JoelEB/ApoBoard2017/PreviousYears/DEFCON_Board/hardware/hhv-dcdarknet-display.brd

## EAGLE design PreviousYears/DEFCON_Board/hardware/hhv-dcdarknet-display.brd (2017-04-06, an earlier design)

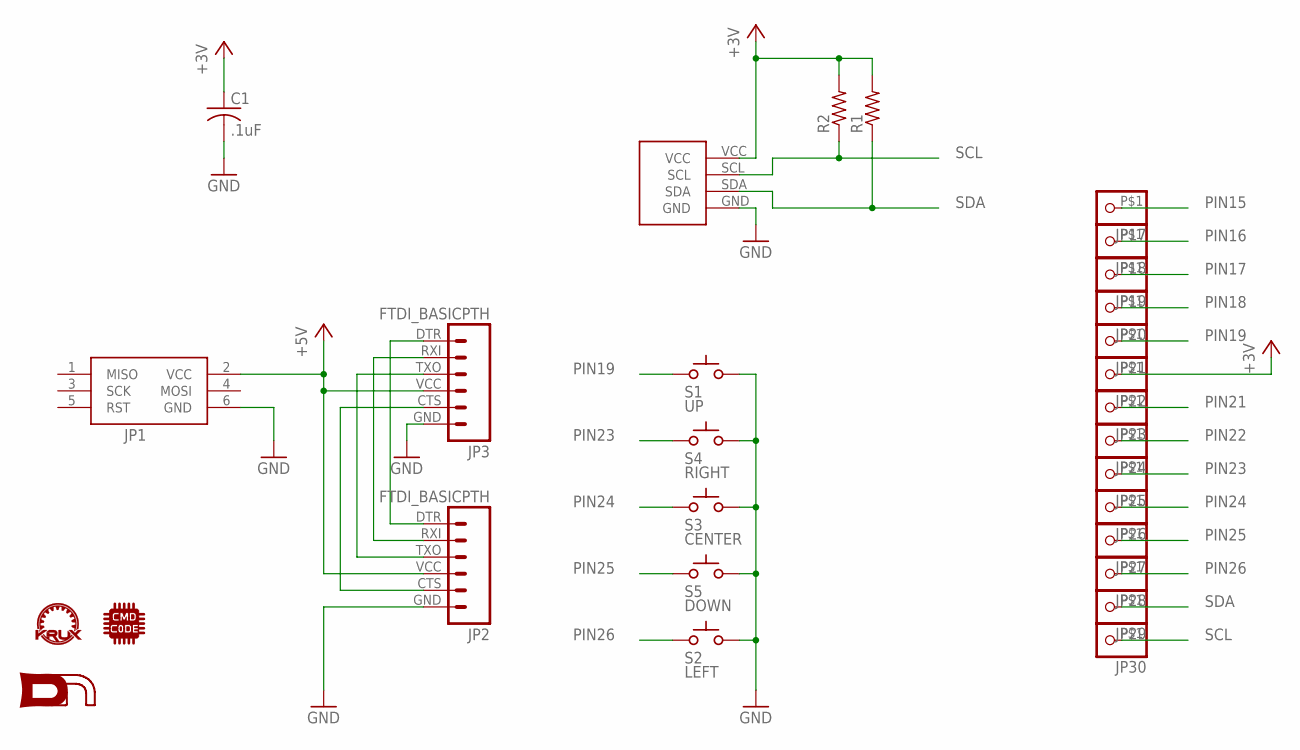
[picture p12: schematic hhv-dcdarknet-display.sch]

Parts:
C1: .1uF; C025-030X050
JP1: JP1; AVRISP
JP2, JP3: FTDI_BASICPTH; FTDI_BASIC
JP17, JP18, JP19, JP20, JP21, JP22, JP23, JP24, JP25, JP26, JP27, JP28, JP29, JP30: PINHD-1X11X1_SQUARE; 1X1-SMALL_CUT
R1, R2: R-US_0204/7; 0204/7
S1: UP; TACTILE-2PIN
S2: LEFT; TACTILE-2PIN
S3: CENTER; TACTILE-2PIN
S4: RIGHT; TACTILE-2PIN
S5: DOWN; TACTILE-2PIN
U$1: KRUX_LOGO
U$2: DN_LOGO
U$3: I2C_0.96_OLEDOLED; I2C_0.96_OLED
U$4: CMDC0DE_LOGO; CMDC0DE

Connections:
+3V3: C1.1, JP22.P$1, R1.2, R2.2, U$3.VCC
+5V: JP1.2 (VCC), JP2.VCC (4), JP3.VCC (4)
GND: C1.2, JP1.6 (GND), JP2.GND (6), JP3.GND (6), S1.P$1 (A), S2.P$1 (A), S3.P$1 (A), S4.P$1 (A), S5.P$1 (A), U$3.GND
unnamed: JP2.DTR (1), JP3.DTR (1)
unnamed: JP2.RXI (2), JP3.RXI (2)
unnamed: JP2.TXO (3), JP3.TXO (3)
unnamed: JP2.CTS (5), JP3.CTS (5)
PIN15: JP17.P$1
PIN16: JP18.P$1
PIN17: JP19.P$1
PIN18: JP20.P$1
PIN19: JP21.P$1, S1.P$2 (C)
PIN21: JP23.P$1
PIN22: JP24.P$1
PIN23: JP25.P$1, S4.P$2 (C)
PIN24: JP26.P$1, S3.P$2 (C)
PIN25: JP27.P$1, S5.P$2 (C)
PIN26: JP28.P$1, S2.P$2 (C)
PIN27: JP29.P$1, R1.1, U$3.SDA
PIN28: JP30.P$1, R2.1, U$3.SCL

Notes on the sheet:
SCL
SDA
PIN26
PIN25
PIN24
PIN23
PIN22
PIN21
PIN19
PIN18
PIN17
PIN16
PIN15

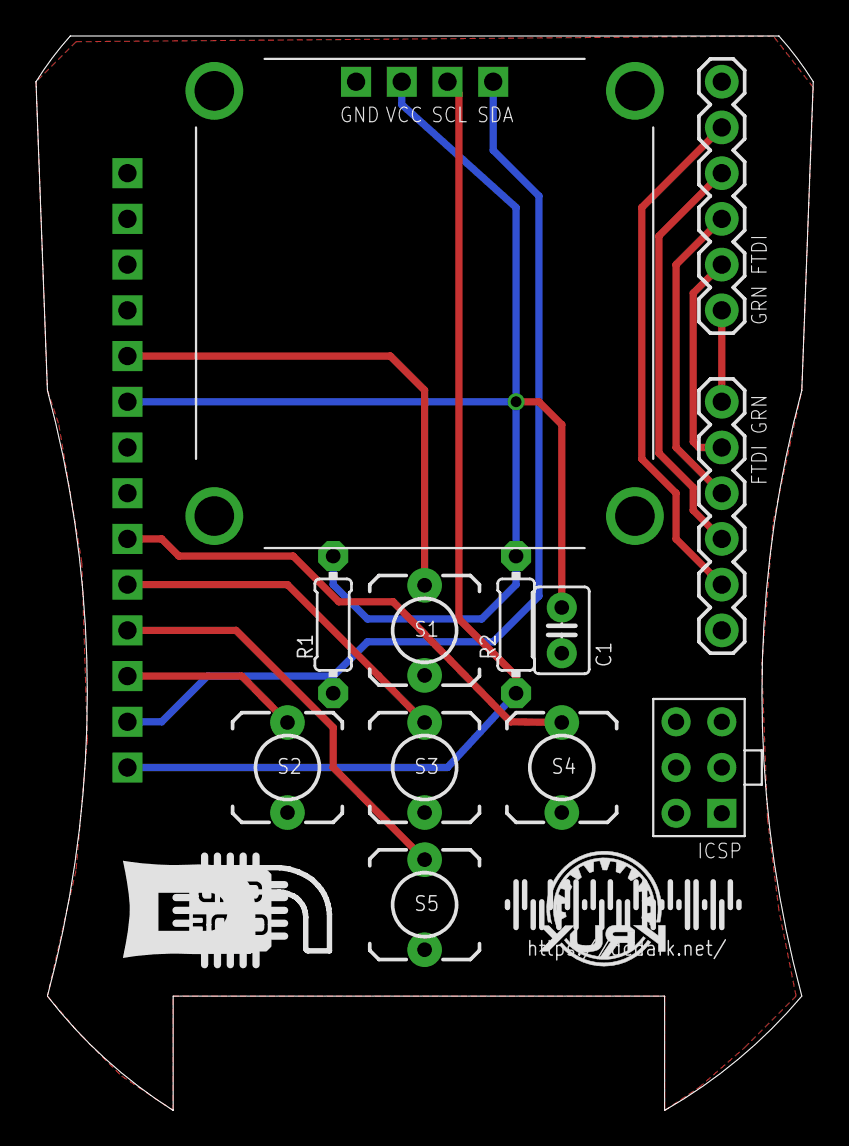
[picture p13: board hhv-dcdarknet-display.brd from above]

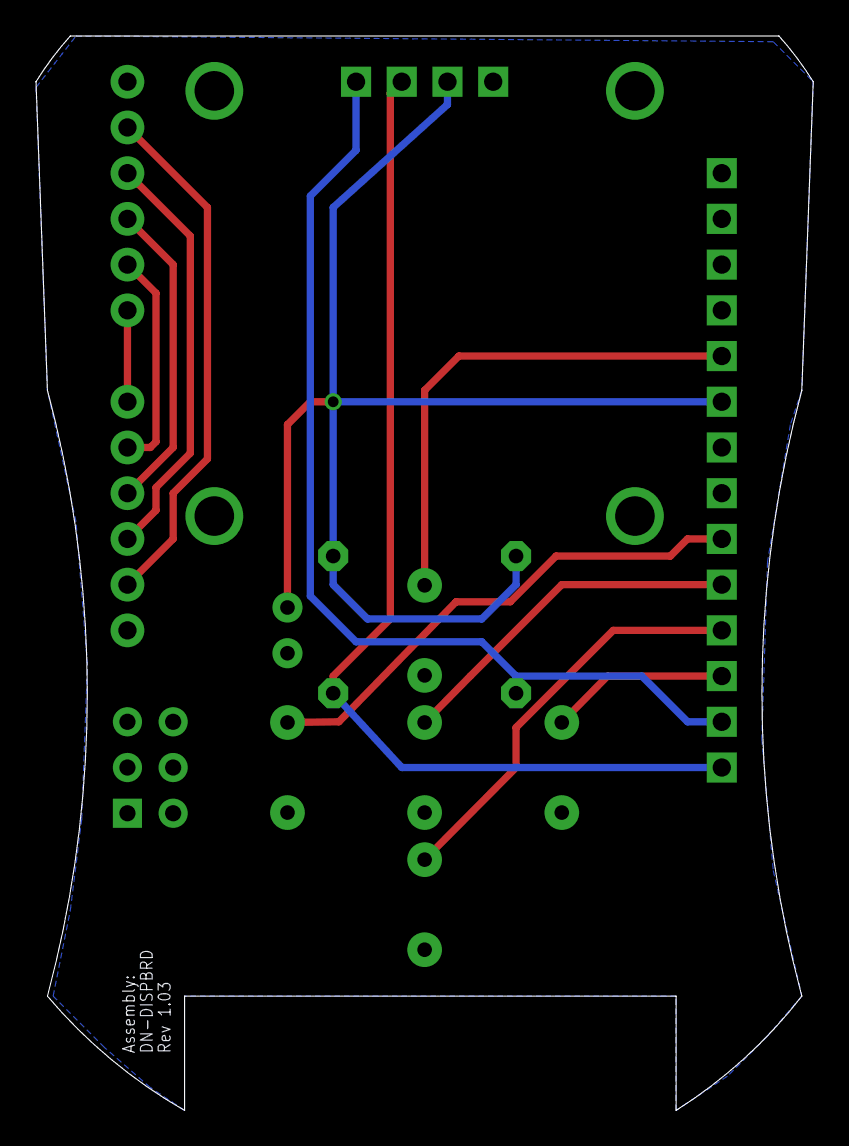
[picture p14: board hhv-dcdarknet-display.brd from below]

Board: 2 copper layers, 43.2 x 59.7 mm, 29 parts (2 on the bottom side), 14 nets.
