JoelEB/ApoBoard2017/PreviousYears/DEFCON_Board/hardware/hhv-dcdarknet-proto.brd

## EAGLE design PreviousYears/DEFCON_Board/hardware/hhv-dcdarknet-proto.brd (2017-04-06, an earlier design)

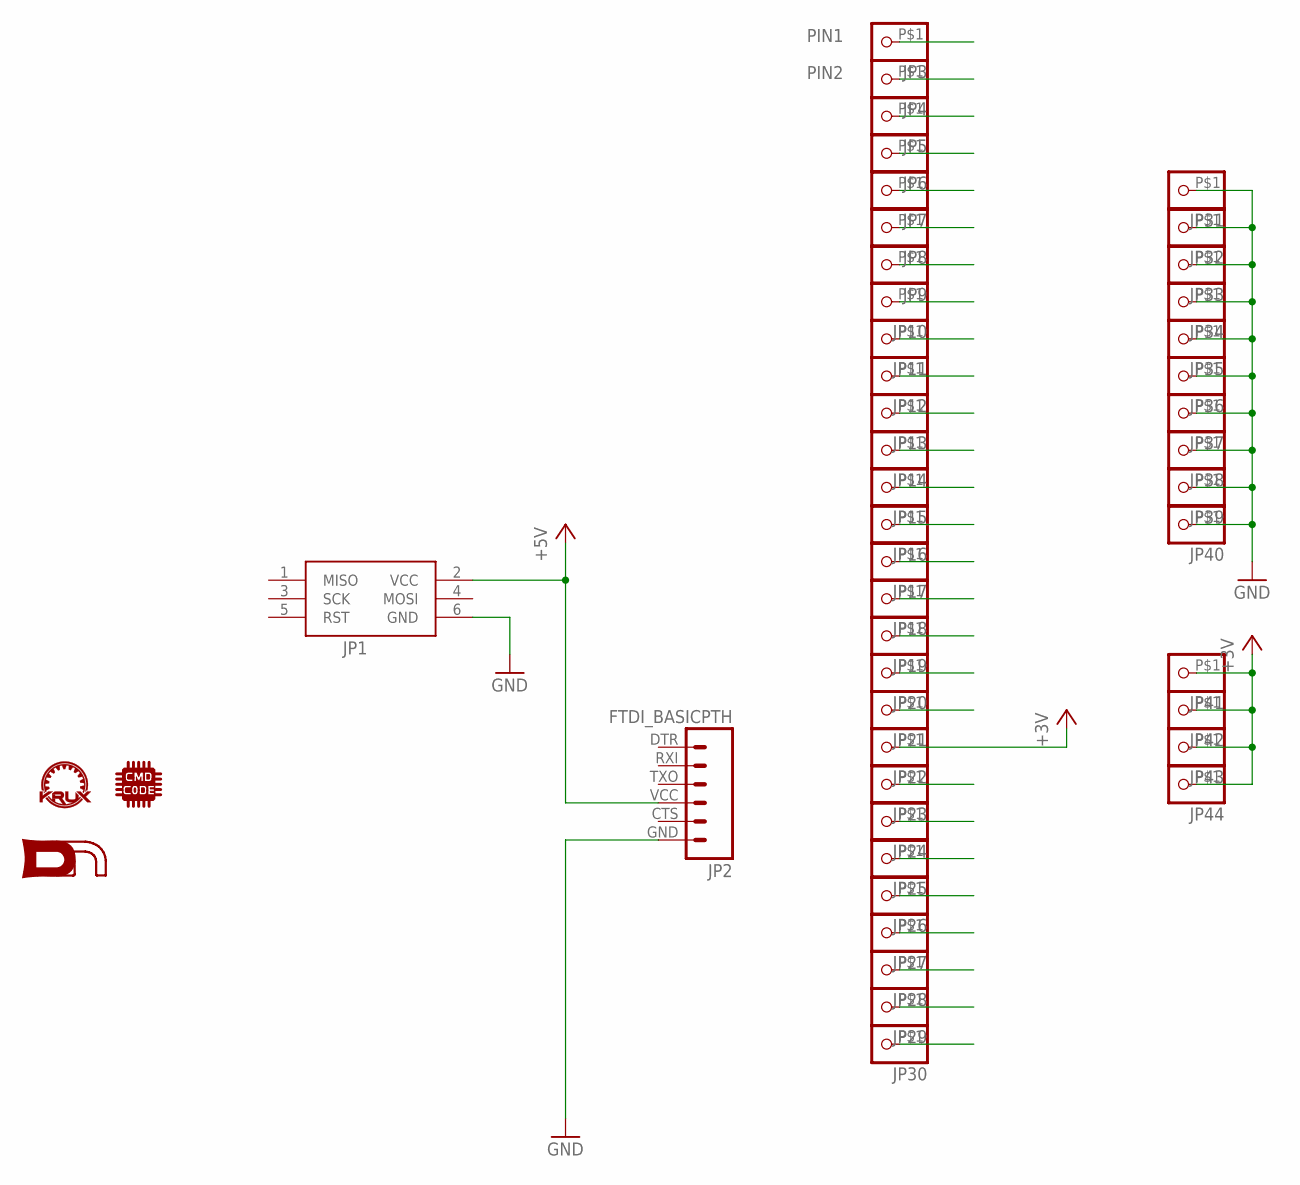
[picture p15: schematic hhv-dcdarknet-proto.sch]

Parts:
JP1: JP1; AVRISP
JP2: FTDI_BASICPTH; FTDI_BASIC
JP3, JP4, JP5, JP6, JP7, JP8, JP9, JP10, JP11, JP12, JP13, JP14, JP15, JP16, JP17, JP18, JP19, JP20, JP21, JP22, JP23, JP24, JP25, JP26, JP27, JP28, JP29, JP30, JP31, JP32, JP33, JP34, JP35, JP36, JP37, JP38, JP39, JP40, JP41, JP42, JP43, JP44: PINHD-1X11X1_SQUARE; 1X1-SMALL_CUT
U$1: KRUX_LOGO
U$2: DN_LOGO
U$3: CMDC0DE_LOGO; CMDC0DE

Connections:
+3V3: JP9.P$1, JP22.P$1, JP41.P$1, JP42.P$1, JP43.P$1, JP44.P$1
+5V: JP1.2 (VCC), JP2.VCC (4)
GND: JP1.6 (GND), JP2.GND (6), JP10.P$1, JP31.P$1, JP32.P$1, JP33.P$1, JP34.P$1, JP35.P$1, JP36.P$1, JP37.P$1, JP38.P$1, JP39.P$1, JP40.P$1
PIN1: JP3.P$1
PIN2: JP4.P$1
PIN3: JP5.P$1
PIN4: JP6.P$1
PIN5: JP7.P$1
PIN6: JP8.P$1
PIN9: JP11.P$1
PIN10: JP12.P$1
PIN11: JP13.P$1
PIN12: JP14.P$1
PIN13: JP15.P$1
PIN14: JP16.P$1
PIN15: JP17.P$1
PIN16: JP18.P$1
PIN17: JP19.P$1
PIN18: JP20.P$1
PIN19: JP21.P$1
PIN21: JP23.P$1
PIN22: JP24.P$1
PIN23: JP25.P$1
PIN24: JP26.P$1
PIN25: JP27.P$1
PIN26: JP28.P$1
PIN27: JP29.P$1
PIN28: JP30.P$1
