JoelEB/ApoBoard2017/PreviousYears/DEFCON_Board/hardware/hhv-dcdarknet-proto.brd

## EAGLE design PreviousYears/DEFCON_Board/hardware/hhv-dcdarknet-proto.brd (continued)

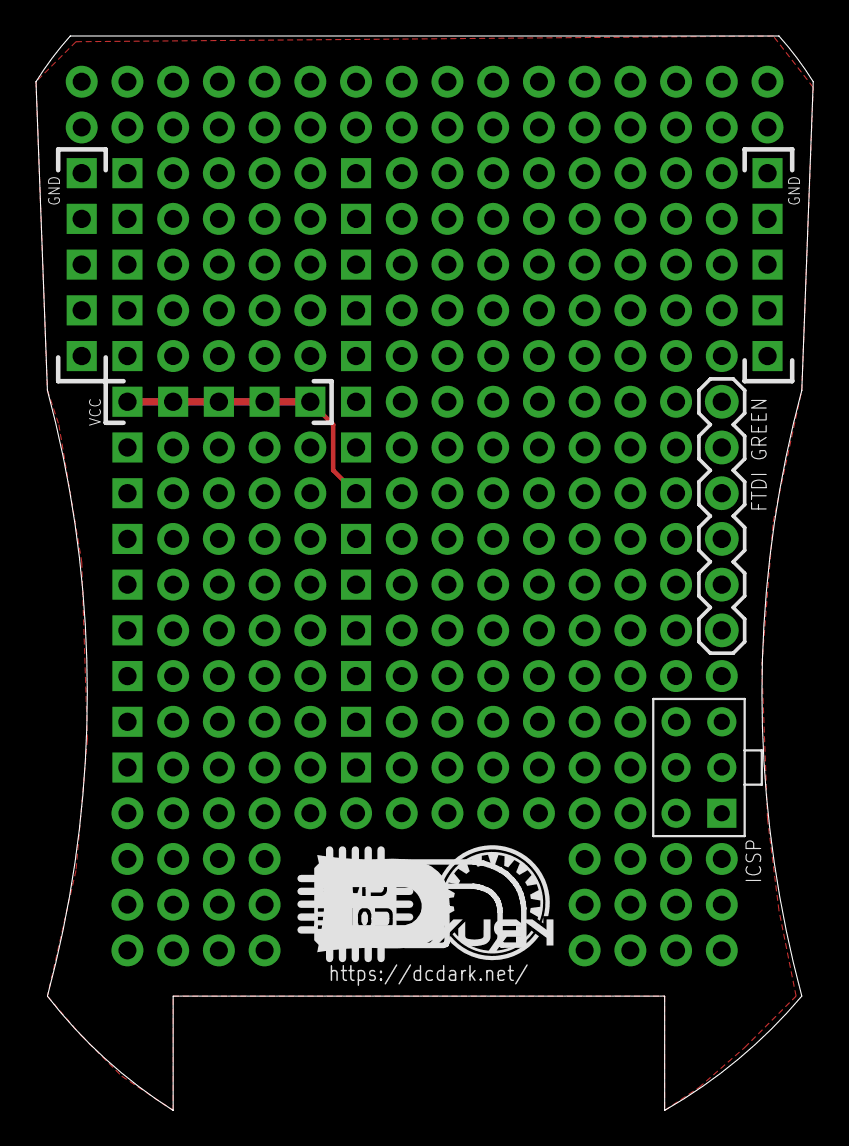
[picture p16: board hhv-dcdarknet-proto.brd from above]

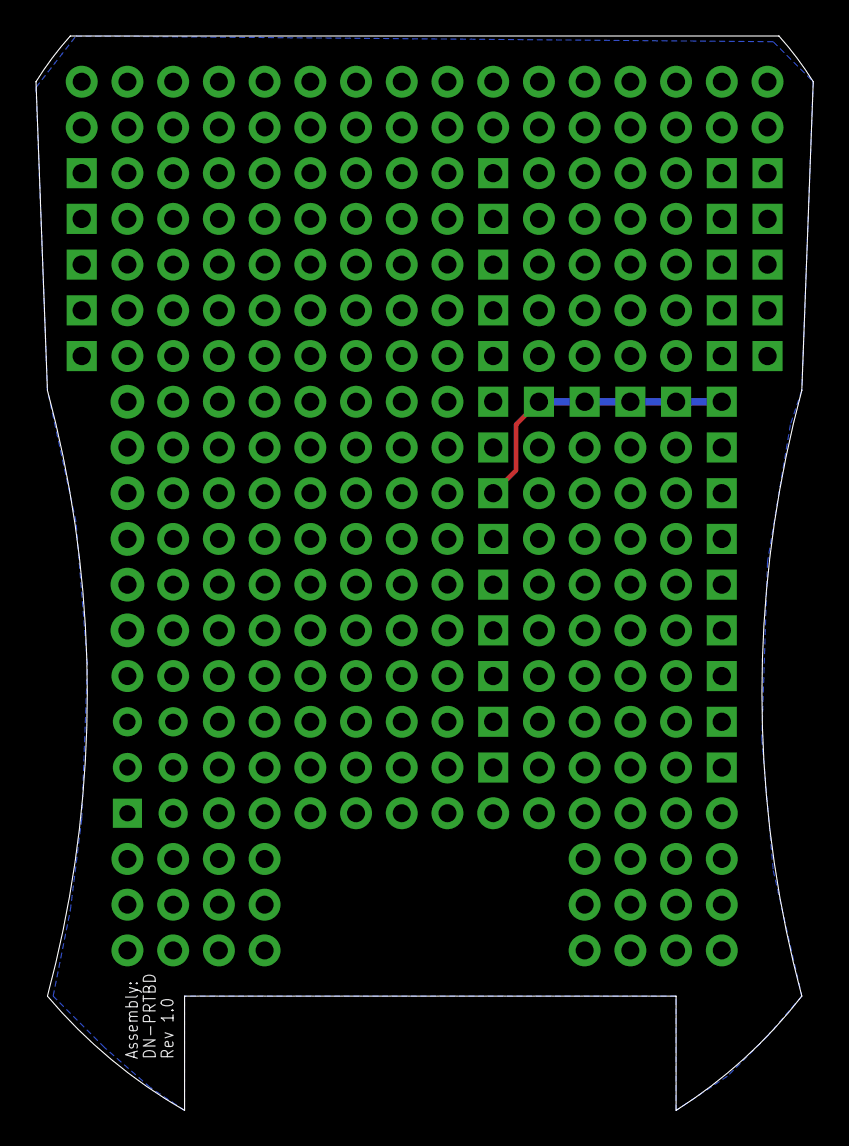
[picture p17: board hhv-dcdarknet-proto.brd from below]

Board: 2 copper layers, 43.2 x 59.7 mm, 47 parts (2 on the bottom side), 3 nets.
