JoelEB/ApoBoard2017/PreviousYears/hardware/apo_board_2014.brd

## EAGLE design PreviousYears/hardware/apo_board_2014.brd (2017-03-08, an earlier design)

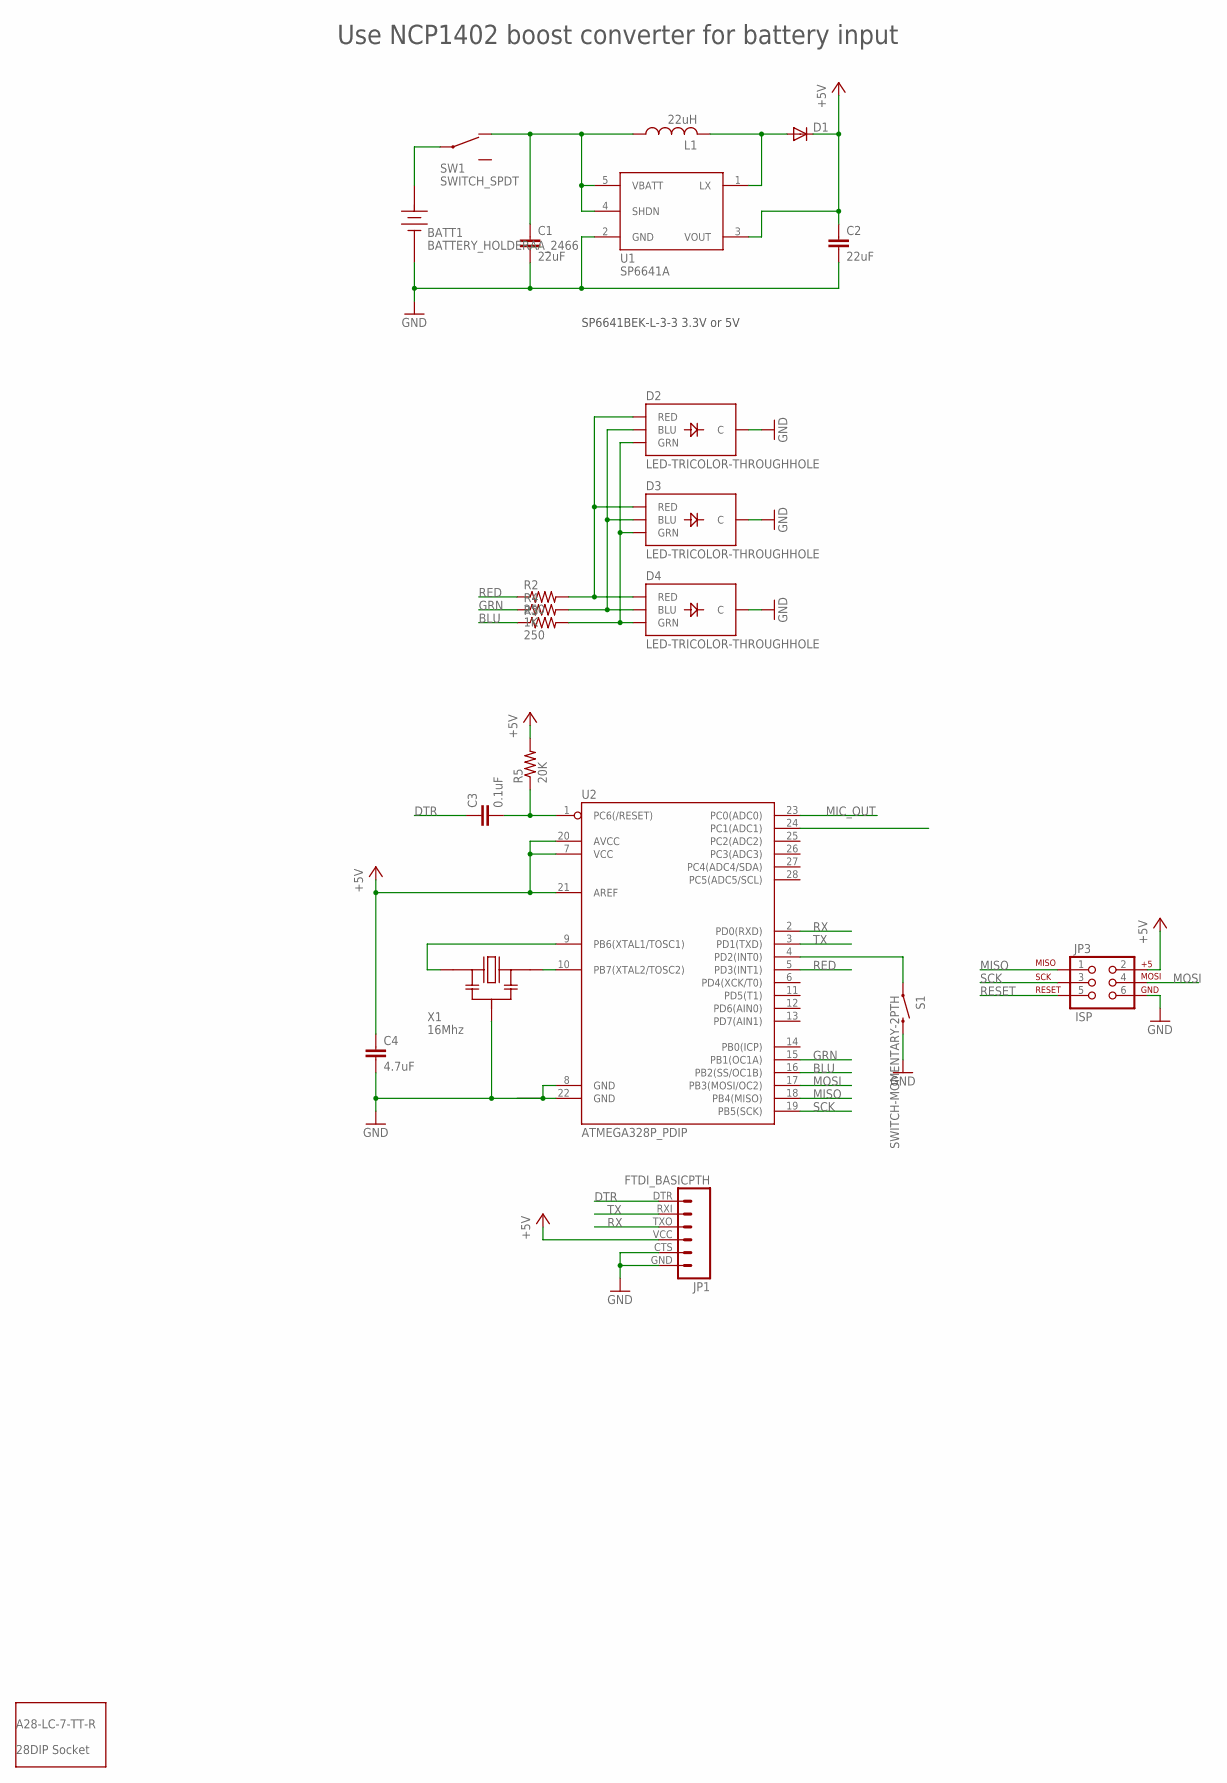
[picture p18: schematic apo_board_2014.sch]

Parts:
BATT1: BATTERY_HOLDERAA_2466; BATT_HOLDER_AA_2466
C1, C2: 22uF; CAP-PTH-SMALL-KIT
C3: 0.1uF; CAP-PTH-SMALL-KIT
C4: 4.7uF; CAP-PTH-SMALL-KIT
D1: DIODEKIT; DIODE-1N4148-KIT
D2, D3, D4: LED-TRICOLOR-THROUGHHOLE
JP1: FTDI_BASICPTH; FTDI_BASIC
JP3: ISP; 2X3
L1: 22uH; INDUCTOR_AIUR-02H
R2, R3: 250; AXIAL-0.3-KIT
R4: 1K; AXIAL-0.3-KIT
R5: 20K; AXIAL-0.3-KIT
S1: SWITCH-MOMENTARY-2PTH; TACTILE-PTH
SW1: SWITCH_SPDT; SWITCH_SPDT_OS102011MA1QN1C
U1: SP6641A; SOT23-5
U2: ATMEGA328P_PDIP; DIL28-3
X1: 16Mhz; CERAMIC_RESONATOR_ZTT

Connections:
+5V: C2.1, C4.1, D1.C, JP1.VCC (4), JP3.2, R5.P$2 (2), U1.3 (VOUT), U2.7 (VCC), U2.20 (AVCC), U2.21 (AREF)
BATT: BATT1.P, SW1.P$2 (COMMON)
BLU: R3.P$1 (1), U2.16 (PB2(SS/OC1B))
DTR: C3.1, JP1.DTR (1)
GND: BATT1.N, C1.2, C2.2, C4.2, D2.GND (C), D3.GND (C), D4.GND (C), JP1.CTS (5), JP1.GND (6), JP3.6, S1.3 (2), U1.2 (GND), U2.8 (GND), U2.22 (GND), X1.P$2
GRN: R4.P$1 (1), U2.15 (PB1(OC1A))
MIC_OUT: U2.23 (PC0(ADC0))
MISO: JP3.1, U2.18 (PB4(MISO))
MOSI: JP3.4, U2.17 (PB3(MOSI/OC2))
unnamed: U2.9 (PB6(XTAL1/TOSC1)), X1.P$1
unnamed: U2.10 (PB7(XTAL2/TOSC2)), X1.P$3
unnamed: S1.1, U2.4 (PD2(INT0))
unnamed: D2.GRN, D3.GRN, D4.GRN, R3.P$2 (2)
unnamed: D2.BLU, D3.BLU, D4.BLU, R4.P$2 (2)
unnamed: C3.2, R5.P$1 (1), U2.1 (PC6(/RESET))
unnamed: D2.RED, D3.RED, D4.RED, R2.P$2 (2)
unnamed: D1.A, L1.P$2 (2), U1.1 (LX)
unnamed: C1.1, L1.P$1 (1), SW1.P$3 (3), U1.4 (SHDN), U1.5 (VBATT)
RED: R2.P$1 (1), U2.5 (PD3(INT1))
RESET: JP3.5
RX: JP1.TXO (3), U2.2 (PD0(RXD))
SCK: JP3.3, U2.19 (PB5(SCK))
TX: JP1.RXI (2), U2.3 (PD1(TXD))

Notes on the sheet:
Use NCP1402 boost converter for battery input
SP6641BEK-L-3-3 3.3V or 5V

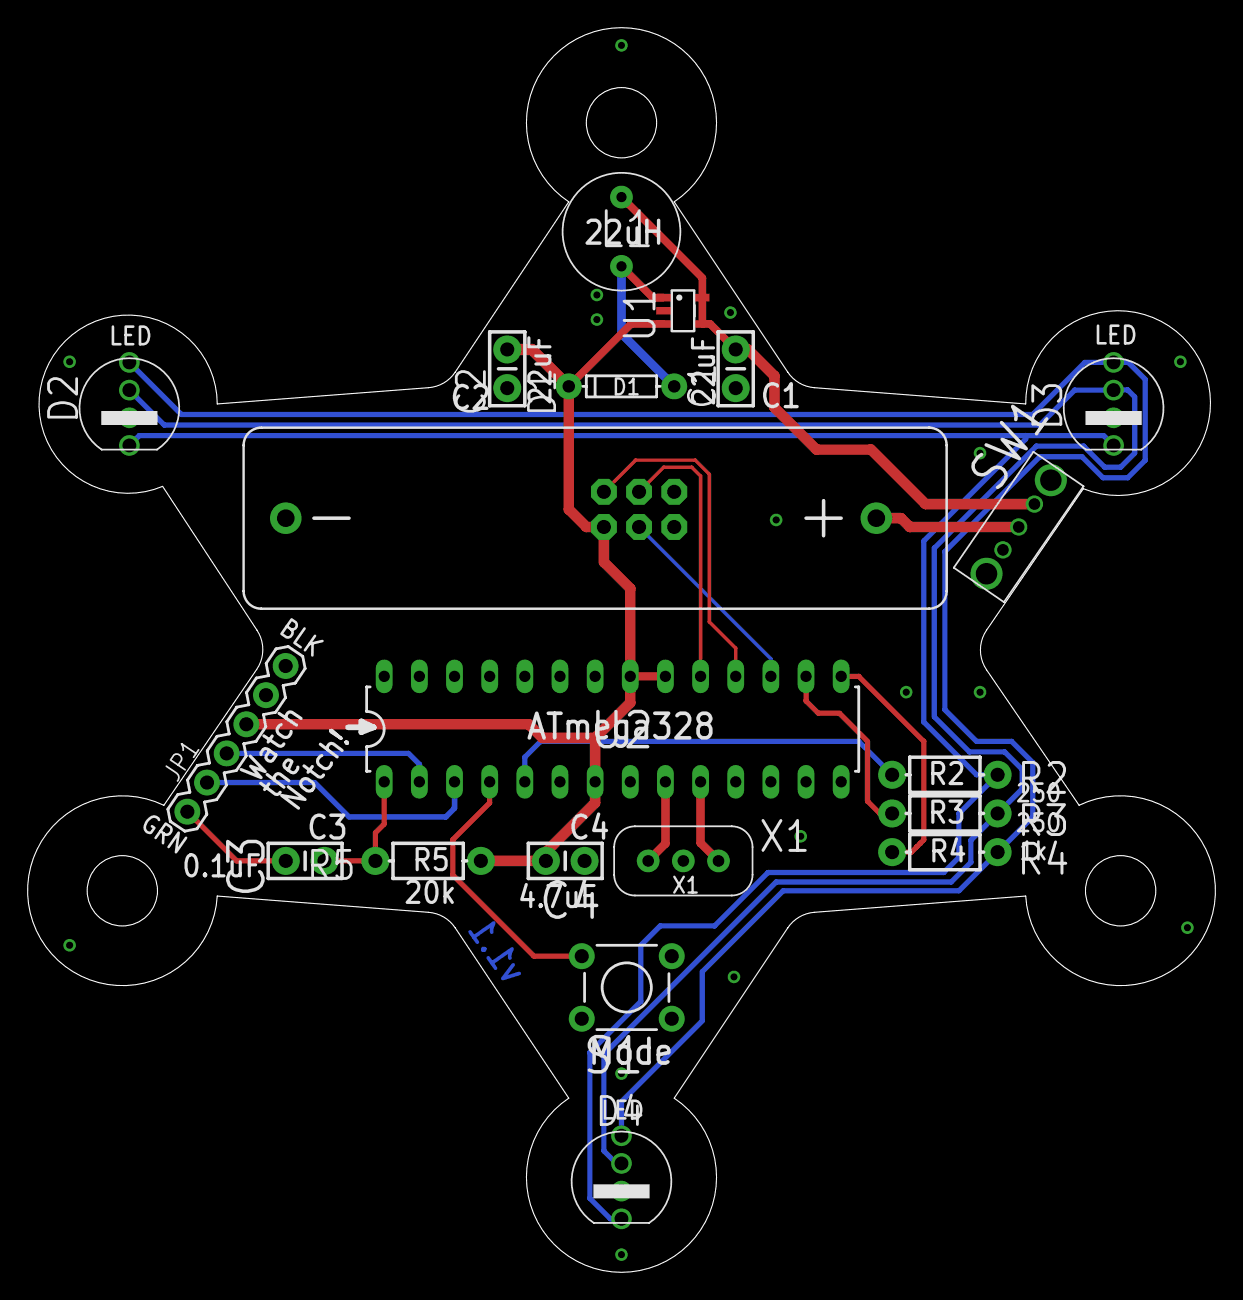
[picture p19: board apo_board_2014.brd from above]

Board: 2 copper layers, 85.8 x 89.9 mm, 21 parts (1 on the bottom side), 21 nets.
