JoelEB/ApoBoard2017/Hardware/Previous Versions/Apo Board 2017 .brd

## EAGLE design Hardware/Previous Versions/Apo Board 2017 .brd (2017-03-08, an earlier design)

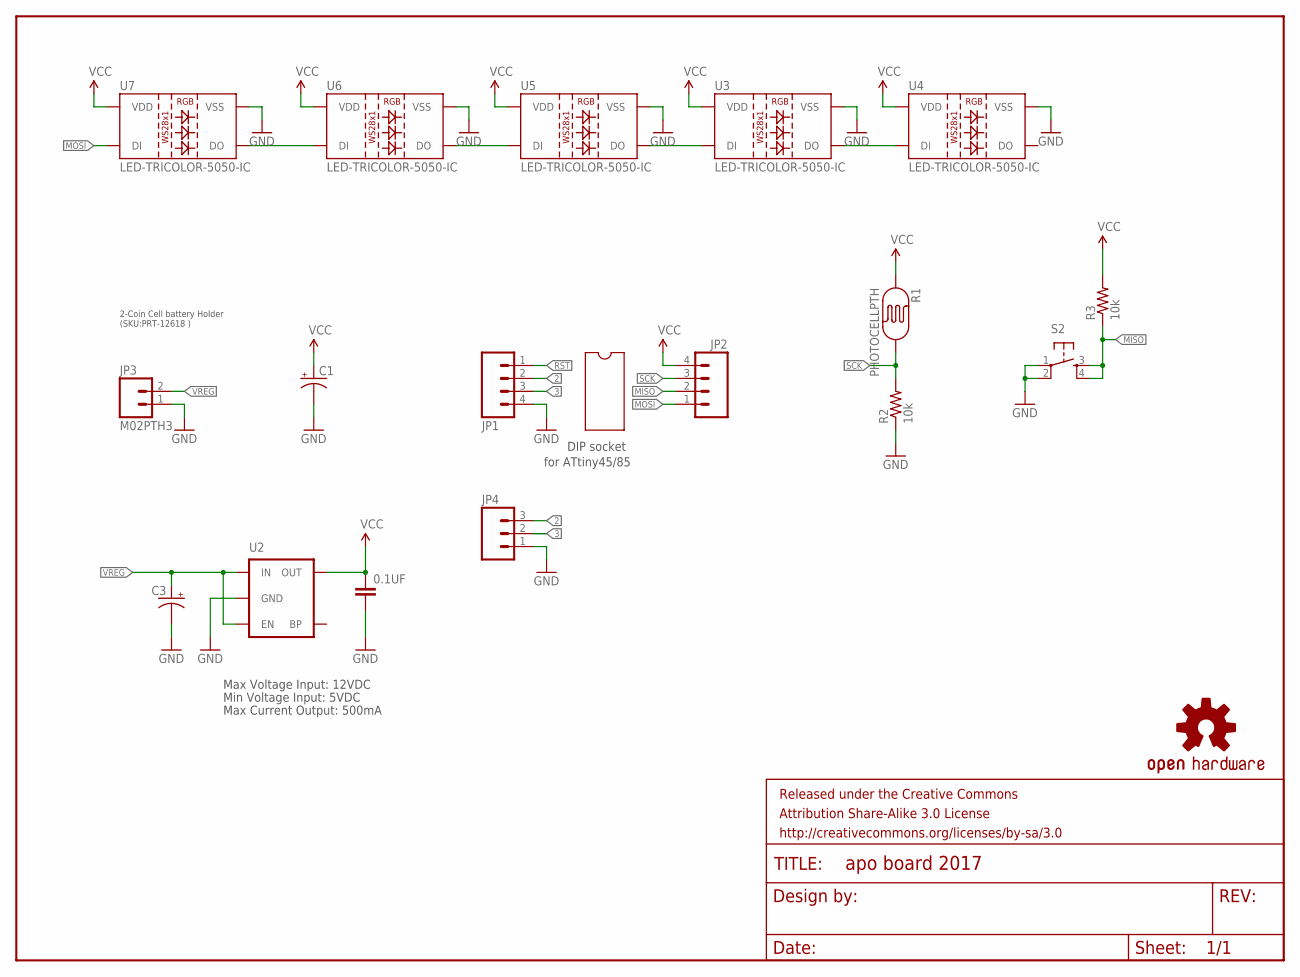
[picture p20: schematic Apo Board 2017 .sch]

Parts:
0.1UF: CAPKIT; CAP-PTH-SMALL-KIT
C1, C3: CAP_POLPTH2; CPOL-RADIAL-10UF-25V
FRAME1: FRAME-LETTER; CREATIVE_COMMONS
JP1, JP2: M04PTH; 1X04
JP3: M02PTH3; 1X02_LONGPADS
JP4: M031X03_NO_SILK; 1X03_NO_SILK
LOGO1: OSHW-LOGOS; OSHW-LOGO-S
R1: PHOTOCELLPTH; PHOTOCELL
R2, R3: 10k; AXIAL-0.4
S2: TAC_SWITCHPTH; TACTILE-PTH
U2: MIC52055V; SOT23-5
U3, U4, U5, U6, U7: LED-TRICOLOR-5050-IC; LED-RGB-THRU

Connections:
2: JP1.2, JP4.3
3: JP1.3, JP4.2
GND: 0.1UF.2, C1.2 (-), C3.2 (-), JP1.4, JP3.1, JP4.1, R2.P$1 (1), S2.1, S2.2, U2.2 (GND), U3.3 (VSS), U4.3 (VSS), U5.3 (VSS), U6.3 (VSS), U7.3 (VSS)
MISO: JP2.2, R3.P$1 (1), S2.3, S2.4
MOSI: JP2.1, U7.1 (DI)
unnamed: U6.1 (DI), U7.4 (DO)
unnamed: U5.1 (DI), U6.4 (DO)
unnamed: U3.1 (DI), U5.4 (DO)
unnamed: U3.4 (DO), U4.1 (DI)
RST: JP1.1
SCK: JP2.3, R1.2, R2.P$2 (2)
VCC: 0.1UF.1, C1.1 (+), JP2.4, R1.1, R3.P$2 (2), U2.5 (OUT), U3.2 (VDD), U4.2 (VDD), U5.2 (VDD), U6.2 (VDD), U7.2 (VDD)
VREG: C3.1 (+), JP3.2, U2.1 (IN), U2.3 (EN)

Notes on the sheet:
DIP socket
for ATtiny45/85
2-Coin Cell battery Holder (SKU:PRT-12618 )
Max Voltage Input: 12VDC
Max Current Output: 500mA
Min Voltage Input: 5VDC

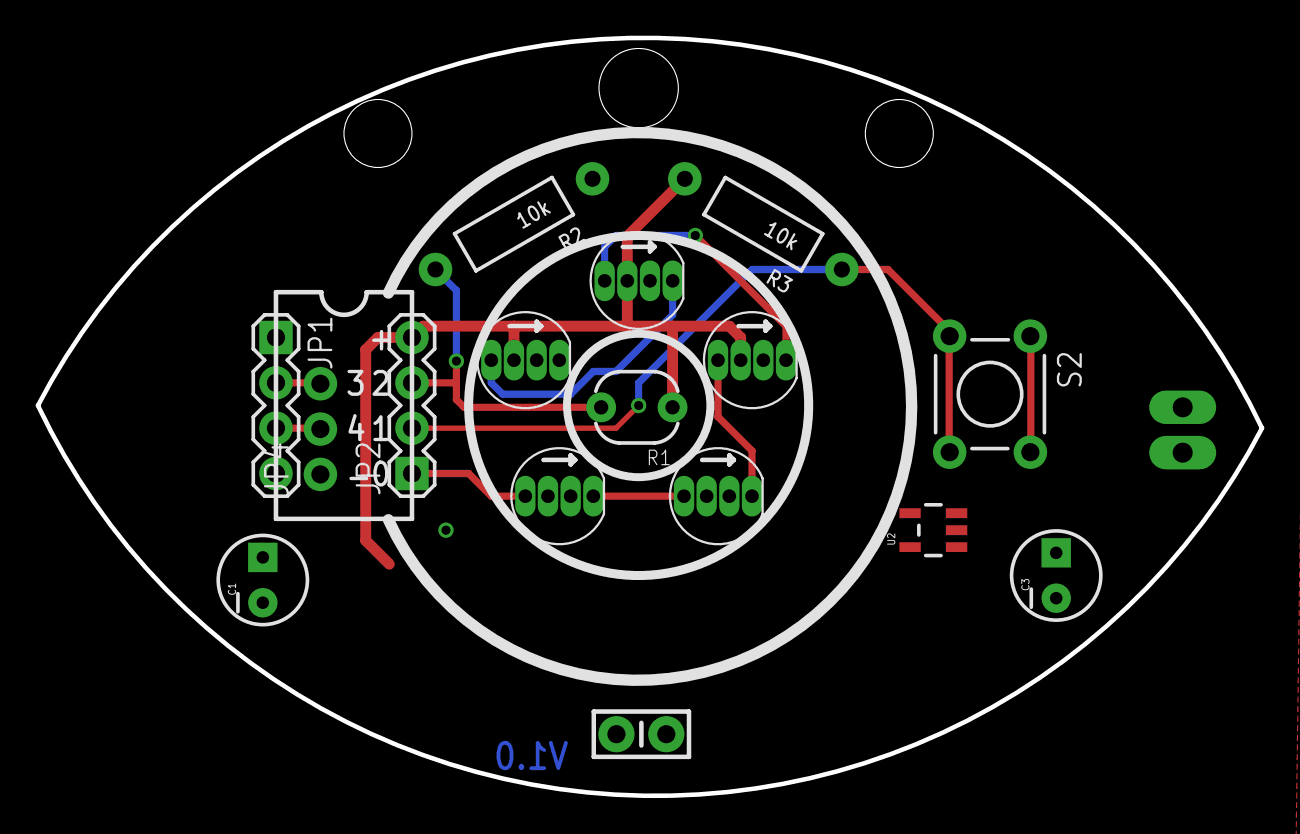
[picture p21: board Apo Board 2017 .brd from above]

Board: 2 copper layers, 68.6 x 42.5 mm, 19 parts (1 on the bottom side), 12 nets.
