JoelEB/ApoBoard2017/Hardware/Previous Versions/Apo Board 2017 ATmega328.brd

## EAGLE design Hardware/Previous Versions/Apo Board 2017 ATmega328.brd (2017-04-04, an earlier design)

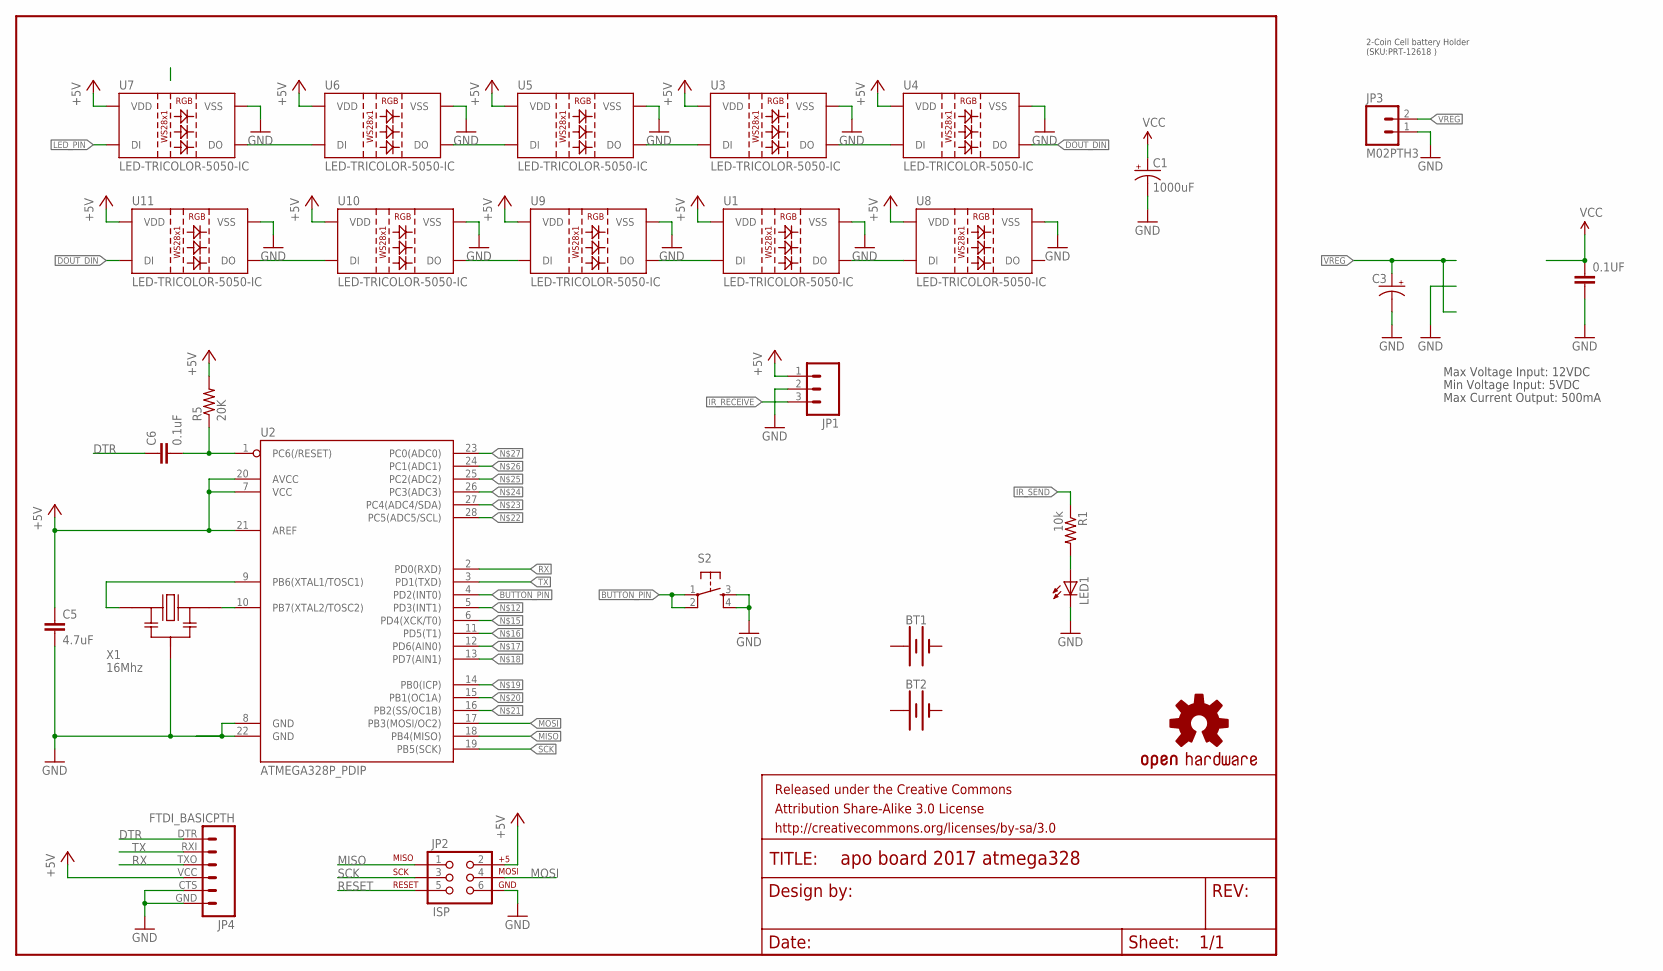
[picture p22: schematic Apo Board 2017 ATmega328.sch]

Parts:
0.1UF: CAPKIT; CAP-PTH-SMALL-KIT
BT1, BT2: BATTERY-AAA
C1: 1000uF; CPOL-RADIAL-10UF-25V
C3: CAP_POLPTH2; CPOL-RADIAL-10UF-25V
C5: 4.7uF; CAP-PTH-SMALL-KIT
C6: 0.1uF; CAP-PTH-SMALL-KIT
FRAME1: FRAME-LETTER; CREATIVE_COMMONS
JP1: M03PTH; 1X03
JP2: ISP; 2X3
JP3: M02PTH3; 1X02_LONGPADS
JP4: FTDI_BASICPTH; FTDI_BASIC
LED1: LED5MM
LOGO1: OSHW-LOGOS; OSHW-LOGO-S
R1: 10k; AXIAL-0.4
R5: 20K; AXIAL-0.3-KIT
S2: TAC_SWITCHPTH; TACTILE-PTH
U1, U3, U4, U5, U6, U7, U8, U9, U10, U11: LED-TRICOLOR-5050-IC; LED-RGB-THRU
U2: ATMEGA328P_PDIP; DIL28-3
X1: 16Mhz; CERAMIC_RESONATOR_ZTT

Connections:
+: BT1.PWR@1 (+), BT2.PWR@1 (+)
+5V: C5.1, JP1.1, JP2.2, JP4.VCC (4), R5.P$2 (2), U1.2 (VDD), U2.7 (VCC), U2.20 (AVCC), U2.21 (AREF), U3.2 (VDD), U4.2 (VDD), U5.2 (VDD), U6.2 (VDD), U7.2 (VDD), U8.2 (VDD), U9.2 (VDD), U10.2 (VDD), U11.2 (VDD)
-: BT1.GND@1 (-), BT2.GND@1 (-)
BUTTON_PIN: S2.1, S2.2, U2.4 (PD2(INT0))
DOUT_DIN: U4.4 (DO), U11.1 (DI)
DTR: C6.1, JP4.DTR (1)
GND: 0.1UF.2, C1.2 (-), C3.2 (-), C5.2, JP1.2, JP2.6, JP3.1, JP4.CTS (5), JP4.GND (6), LED1.K (C), S2.3, S2.4, U1.3 (VSS), U2.8 (GND), U2.22 (GND), U3.3 (VSS), U4.3 (VSS), U5.3 (VSS), U6.3 (VSS), U7.3 (VSS), U8.3 (VSS), U9.3 (VSS), U10.3 (VSS), U11.3 (VSS), X1.P$2
IR_RECEIVE: JP1.3
IR_SEND: R1.P$1 (1)
LED_PIN: U7.1 (DI)
MISO: JP2.1, U2.18 (PB4(MISO))
MOSI: JP2.4, U2.17 (PB3(MOSI/OC2))
unnamed: U6.1 (DI), U7.4 (DO)
unnamed: U5.1 (DI), U6.4 (DO)
unnamed: LED1.A, R1.P$2 (2)
unnamed: U2.9 (PB6(XTAL1/TOSC1)), X1.P$1
unnamed: U3.1 (DI), U5.4 (DO)
unnamed: U3.4 (DO), U4.1 (DI)
unnamed: U2.10 (PB7(XTAL2/TOSC2)), X1.P$3
unnamed: U10.1 (DI), U11.4 (DO)
unnamed: C6.2, R5.P$1 (1), U2.1 (PC6(/RESET))
unnamed: U9.1 (DI), U10.4 (DO)
unnamed: U1.1 (DI), U9.4 (DO)
unnamed: U1.4 (DO), U8.1 (DI)
RESET: JP2.5
RX: JP4.TXO (3), U2.2 (PD0(RXD))
SCK: JP2.3, U2.19 (PB5(SCK))
TX: JP4.RXI (2), U2.3 (PD1(TXD))
VCC: 0.1UF.1, C1.1 (+)
VREG: C3.1 (+), JP3.2

Notes on the sheet:
2-Coin Cell battery Holder (SKU:PRT-12618 )
Max Voltage Input: 12VDC
Max Current Output: 500mA
Min Voltage Input: 5VDC

Board: 2 copper layers, 29 parts (1 on the bottom side), 26 nets, no tracks yet.
