JoelEB/ApoBoard2017/Hardware/Previous Versions/Tiny_Programmer_v13.brd

## EAGLE design Hardware/Previous Versions/Tiny_Programmer_v13.brd (2017-03-08, an earlier design)

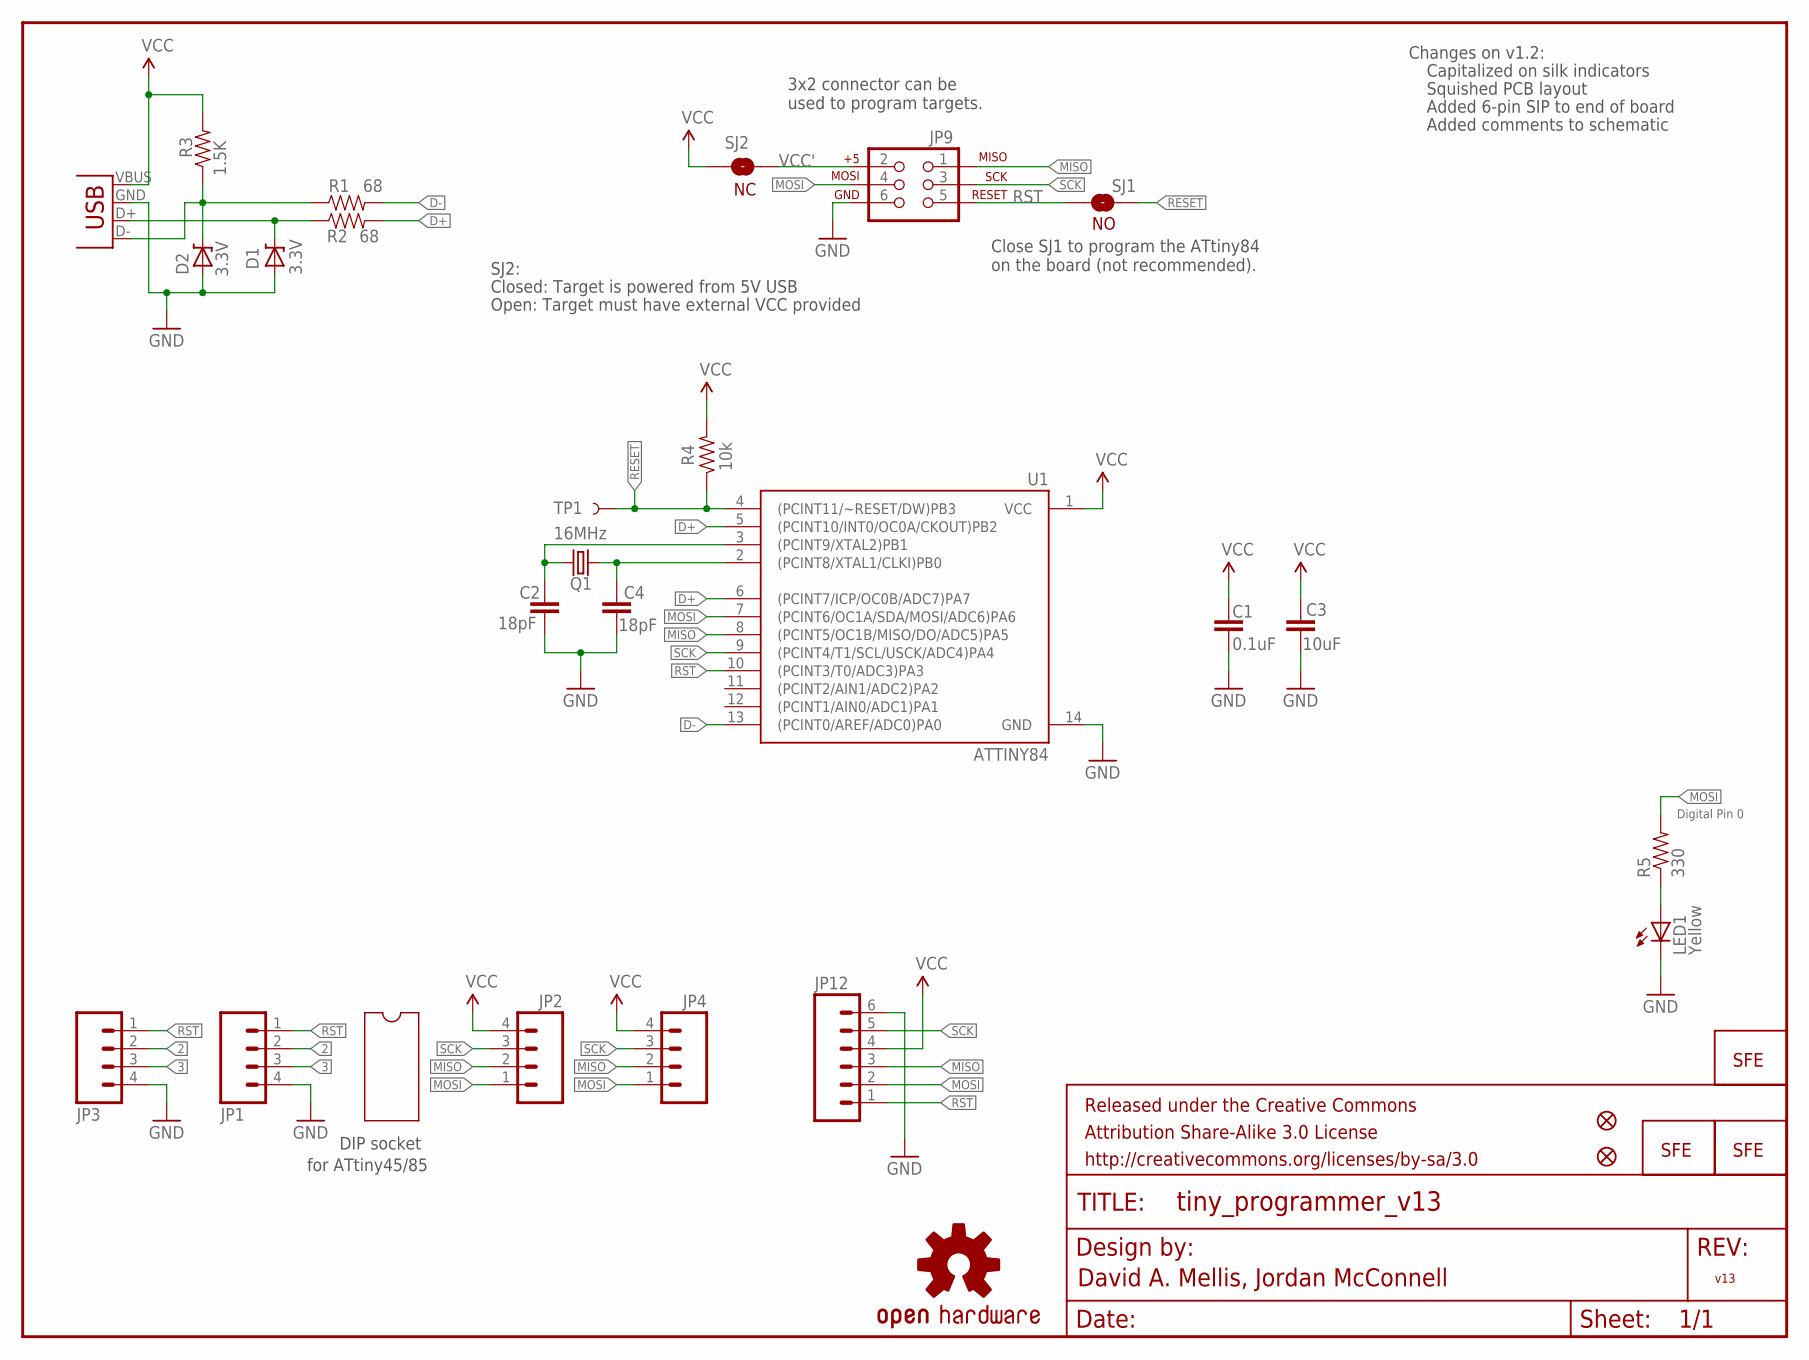
[picture p23: schematic Tiny_Programmer_v13.sch]

Parts:
C1: 0.1uF; 0402-CAP
C2, C4: 18pF; 0402-CAP
C3: 10uF; 0402-CAP
D1, D2: 3.3V; SOD-323
FRAME1: FRAME-LETTER; CREATIVE_COMMONS
JP1, JP2: M04PTH; 1X04
JP3, JP4: M04SMD_STRAIGHT_COMBO; 1X04_SMD_STRAIGHT_COMBO
JP5: LOGO-SFENW2; SFE-NEW-WEB
JP6, JP11: LOGO-SFESK; SFE-LOGO-FLAME
JP7, JP8: FIDUCIALUFIDUCIAL; MICRO-FIDUCIAL
JP9: AVR_SPI_PRG_6PTH; 2X3
JP12: M06SIP; 1X06
LED1: Yellow; LED-0603
Q1: 16MHz; CRYSTAL-SMD-5X3
R1, R2: 68; 0402-RES
R3: 1.5K; 0402-RES
R4: 10k; 0402-RES
R5: 330; 0402-RES
SJ1: SOLDERJUMPERNO; SJ_2S-NO
SJ2: NC; SJ_2S
TP1: TEST-POINT3; PAD.03X.03
U1: ATTINY84; SO14
U$1: OSHW-LOGOS; OSHW-LOGO-S
X1: USB-A-H

Connections:
2: JP1.2, JP3.2
3: JP1.3, JP3.3
D+: R2.2, U1.5 ((PCINT10/INT0/OC0A/CKOUT)PB2), U1.6 ((PCINT7/ICP/OC0B/ADC7)PA7)
D-: R1.2, U1.13 ((PCINT0/AREF/ADC0)PA0)
GND: C1.2, C2.2, C3.2, C4.2, D1.2 (A), D2.2 (A), JP1.4, JP3.4, JP9.6, JP12.6, LED1.C, U1.14 (GND), X1.GND (VBUS)
MISO: JP2.2, JP4.2, JP9.1, JP12.3, U1.8 ((PCINT5/OC1B/MISO/DO/ADC5)PA5)
MOSI: JP2.1, JP4.1, JP9.4, JP12.2, R5.2, U1.7 ((PCINT6/OC1A/SDA/MOSI/ADC6)PA6)
unnamed: D2.1 (C), R1.1, R3.1, X1.D- (D+)
unnamed: D1.1 (C), R2.1, X1.D+ (D-)
unnamed: C2.1, Q1.3 (2), U1.3 ((PCINT9/XTAL2)PB1)
unnamed: C4.1, Q1.1, U1.2 ((PCINT8/XTAL1/CLKI)PB0)
unnamed: LED1.A, R5.1
RESET: R4.1, SJ1.1, TP1.P$1, U1.4 ((PCINT11/~RESET/DW)PB3)
RST: JP1.1, JP3.1, JP9.5, JP12.1, SJ1.2, U1.10 ((PCINT3/T0/ADC3)PA3)
SCK: JP2.3, JP4.3, JP9.3, JP12.5, U1.9 ((PCINT4/T1/SCL/USCK/ADC4)PA4)
VCC: C1.1, C3.1, JP2.4, JP4.4, JP12.4, R3.2, R4.2, SJ2.1, U1.1 (VCC), X1.VBUS (GND)
VCC': JP9.2, SJ2.2

Notes on the sheet:
David A. Mellis, Jordan McConnell
Digital Pin 0
Changes on v1.2:
Capitalized on silk indicators
DIP socket
for ATtiny45/85
3x2 connector can be used to program targets.
Close SJ1 to program the ATtiny84 on the board (not recommended).
Closed: Target is powered from 5V USB
Open: Target must have external VCC provided
SJ2:
Squished PCB layout
Added 6-pin SIP to end of board
Added comments to schematic
v13

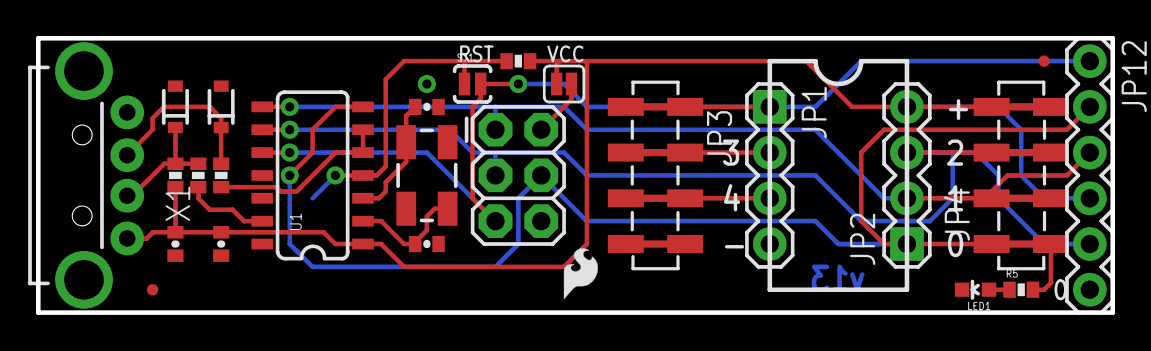
[picture p24: board Tiny_Programmer_v13.brd from above]

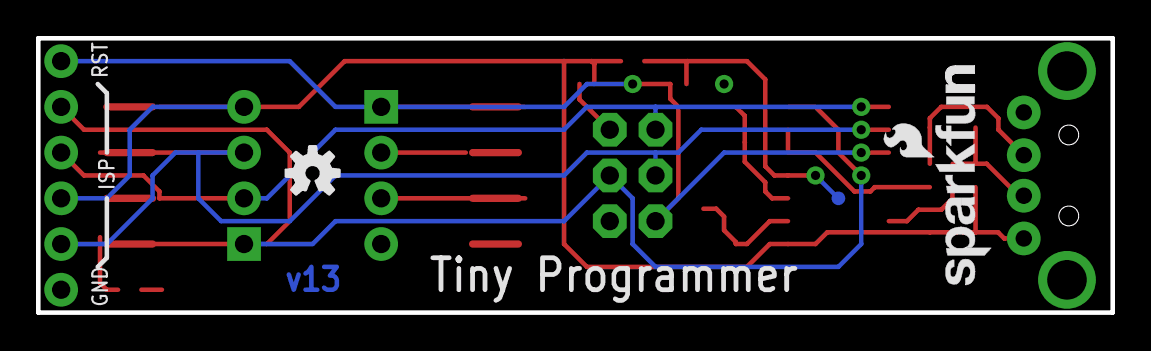
[picture p25: board Tiny_Programmer_v13.brd from below]

Board: 2 copper layers, 59.7 x 15.2 mm, 31 parts (4 on the bottom side), 17 nets.
