JoelEB/ApoBoard2017/Firmware/ApoBoardTest/ApoBoardTest.ino

#include <Adafruit_NeoPixel.h>
#include <avr/power.h> // Comment out this line for non-AVR boards (Arduino Due, etc.)


#include <SoftwareSerial.h>

SoftwareSerial mySerial(4, 3); // RX, TX
//for debug

#define PIN 1
#define LEDs 5

int button = 1;
int photopot = A1;
int colorModeMax = 5; 
int colorMode = 0;


// Parameter 1 = number of pixels in strip
// Parameter 2 = Arduino pin number (most are valid)
// Parameter 3 = pixel type flags, add together as needed:
//   NEO_KHZ800  800 KHz bitstream (most NeoPixel products w/WS2812 LEDs)
//   NEO_KHZ400  400 KHz (classic 'v1' (not v2) FLORA pixels, WS2811 drivers)
//   NEO_GRB     Pixels are wired for GRB bitstream (most NeoPixel products)
//   NEO_RGB     Pixels are wired for RGB bitstream (v1 FLORA pixels, not v2)
Adafruit_NeoPixel strip = Adafruit_NeoPixel(LEDs, PIN, NEO_GRB + NEO_KHZ800);

// IMPORTANT: To reduce NeoPixel burnout risk, add 1000 uF capacitor across
// pixel power leads, add 300 - 500 Ohm resistor on first pixel's data input
// and minimize distance between Arduino and first pixel.  Avoid connecting
// on a live circuit...if you must, connect GND first.

 
// Here is where you can put in your favorite colors that will appear!
// just add new {nnn, nnn, nnn}, lines. They will be picked out randomly
//                          R   G   B
uint8_t myColors[][3] = {{232, 100, 255},   // purple
                         {200, 200, 20},   // yellow 
                         {30, 200, 200},   // blue
                          };
#define FAVCOLORS sizeof(myColors) / 3

void setup() 
{
  
  mySerial.begin(9600);

  pinMode(button, INPUT);
  pinMode(photopot, INPUT);
  strip.begin();

  strip.setBrightness(40);

  strip.show(); // Initialize all pixels to 'off'
}



void loop() 
{

  int temp = analogRead(photopot);
    if(temp >900)
  rainbowCycle(2);
/*

  else if(temp < 200)
  colorWipe(strip.Color(255, 0, 0), 50); // Red

  if(temp < 20)
  colorWipe(strip.Color(0, 255, 0), 10); // Red
*/
  
  // Some example procedures showing how to display to the pixels:
  //colorWipe(strip.Color(255, 0, 0), 50); // Red
  //colorWipe(strip.Color(0, 255, 0), 50); // Green
  //colorWipe(strip.Color(0, 0, 255), 50); // Blue
  // Send a theater pixel chase in...
  //theaterChase(strip.Color(127, 127, 127), 50); // White
  //theaterChase(strip.Color(127,   0,   0), 50); // Red
  //theaterChase(strip.Color(  0,   0, 127), 50); // Blue

  //rainbow(20);
  //rainbowCycle(20);
 // theaterChaseRainbow(50);

flashRandom(5, 1);  // first number is 'wait' delay, shorter num == shorter twinkle
flashRandom(5, 3);  // second number is how many neopixels to simultaneously light up
flashRandom(5, 2);

/*
 if(!digitalRead(button))
 {
  colorMode++;
  if(colorMode > colorModeMax)
  {
    colorMode = 0;
  }
  delay(150);
 }
 checkColorMode();


 mySerial.print("Mode: ");
 mySerial.print(colorMode);
 mySerial.print(" | temp: ");
 mySerial.println(temp);
 */
}
///////////////////////////////////////
void checkColorMode()
{
  if(colorMode == 0)
  {
    colorWipe(strip.Color(0, 255, 0), 50);//green
  } 
  if(colorMode == 1)
  {
    colorWipe(strip.Color(125, 125, 0), 50);//yellow
  } 
  if(colorMode == 2)
  {
    colorWipe(strip.Color(255, 0, 0), 50);//Red
  } 
  if(colorMode == 3)
  {
    colorWipe(strip.Color(125, 0, 125), 50);//purple
  } 
  if(colorMode == 4)
  {
    colorWipe(strip.Color(0, 0, 255), 50);//blue
  } 
  if(colorMode == 5)
  {
    colorWipe(strip.Color(0, 125, 125), 50);//cyan
  } 
  
}
// Fill the dots one after the other with a color
void colorWipe(uint32_t c, uint8_t wait) {
  for(uint16_t i=0; i<strip.numPixels(); i++) {
      strip.setPixelColor(i, c);
      strip.show();
      delay(wait);
  }
}

void rainbow(uint8_t wait) {
  uint16_t i, j;

  for(j=0; j<256; j++) {
    for(i=0; i<strip.numPixels(); i++) {
      strip.setPixelColor(i, Wheel((i+j) & 255));
    }
    strip.show();
    delay(wait);
  }
}

// Slightly different, this makes the rainbow equally distributed throughout
void rainbowCycle(uint8_t wait) {
  uint16_t i, j;

  for(j=0; j<256*5; j++) { // 5 cycles of all colors on wheel
    for(i=0; i< strip.numPixels(); i++) {
      strip.setPixelColor(i, Wheel(((i * 256 / strip.numPixels()) + j) & 255));
    }
    strip.show();
    delay(wait);
  }
}

//Theatre-style crawling lights.
void theaterChase(uint32_t c, uint8_t wait) {
  for (int j=0; j<10; j++) {  //do 10 cycles of chasing
    for (int q=0; q < 3; q++) {
      for (int i=0; i < strip.numPixels(); i=i+3) {
        strip.setPixelColor(i+q, c);    //turn every third pixel on
      }
      strip.show();
     
      delay(wait);
     
      for (int i=0; i < strip.numPixels(); i=i+3) {
        strip.setPixelColor(i+q, 0);        //turn every third pixel off
      }
    }
  }
}

//Theatre-style crawling lights with rainbow effect
void theaterChaseRainbow(uint8_t wait) {
  for (int j=0; j < 256; j++) {     // cycle all 256 colors in the wheel
    for (int q=0; q < 3; q++) {
        for (int i=0; i < strip.numPixels(); i=i+3) {
          strip.setPixelColor(i+q, Wheel( (i+j) % 255));    //turn every third pixel on
        }
        strip.show();
       
        delay(wait);
       
        for (int i=0; i < strip.numPixels(); i=i+3) {
          strip.setPixelColor(i+q, 0);        //turn every third pixel off
        }
    }
  }
}

// Input a value 0 to 255 to get a color value.
// The colours are a transition r - g - b - back to r.
uint32_t Wheel(byte WheelPos) {
  WheelPos = 255 - WheelPos;
  if(WheelPos < 85) {
   return strip.Color(255 - WheelPos * 3, 0, WheelPos * 3);
  } else if(WheelPos < 170) {
    WheelPos -= 85;
   return strip.Color(0, WheelPos * 3, 255 - WheelPos * 3);
  } else {
   WheelPos -= 170;
   return strip.Color(WheelPos * 3, 255 - WheelPos * 3, 0);
  }
}

void flashRandom(int wait, uint8_t howmany) {
 
  for(uint16_t i=0; i<howmany; i++) {
    // pick a random favorite color!
    int c = random(FAVCOLORS);
    int red = myColors[c][0];
    int green = myColors[c][1];
    int blue = myColors[c][2]; 
 
    // get a random pixel from the list
    int j = random(strip.numPixels());
    
    // now we will 'fade' it in 5 steps
    for (int x=0; x < 5; x++) {
      int r = red * (x+1); r /= 5;
      int g = green * (x+1); g /= 5;
      int b = blue * (x+1); b /= 5;
      
      strip.setPixelColor(j, strip.Color(r, g, b));
      strip.show();
      delay(wait);
    }
    // & fade out in 5 steps
    for (int x=5; x >= 0; x--) {
      int r = red * x; r /= 5;
      int g = green * x; g /= 5;
      int b = blue * x; b /= 5;
      
      strip.setPixelColor(j, strip.Color(r, g, b));
      strip.show();
      delay(wait);
    }
  }
  // LEDs will be off when done (they are faded to 0)
}
